VaiOnko/gould-k20/pictures/exterior/bottom.jpg

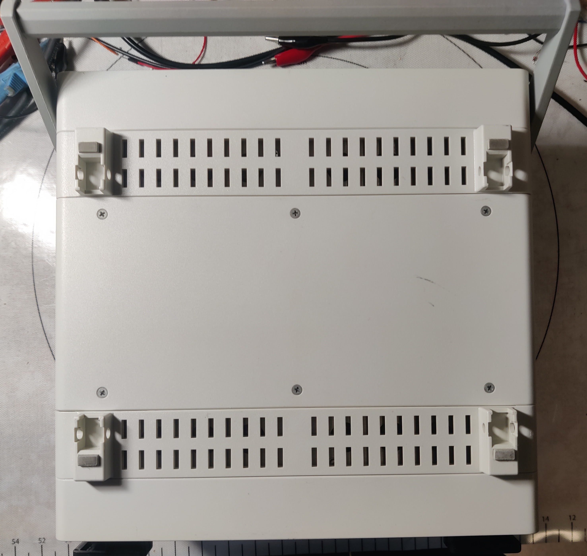
pictures/exterior/bottom.jpg
