VaiOnko/gould-k20/pictures/exterior/top.jpg

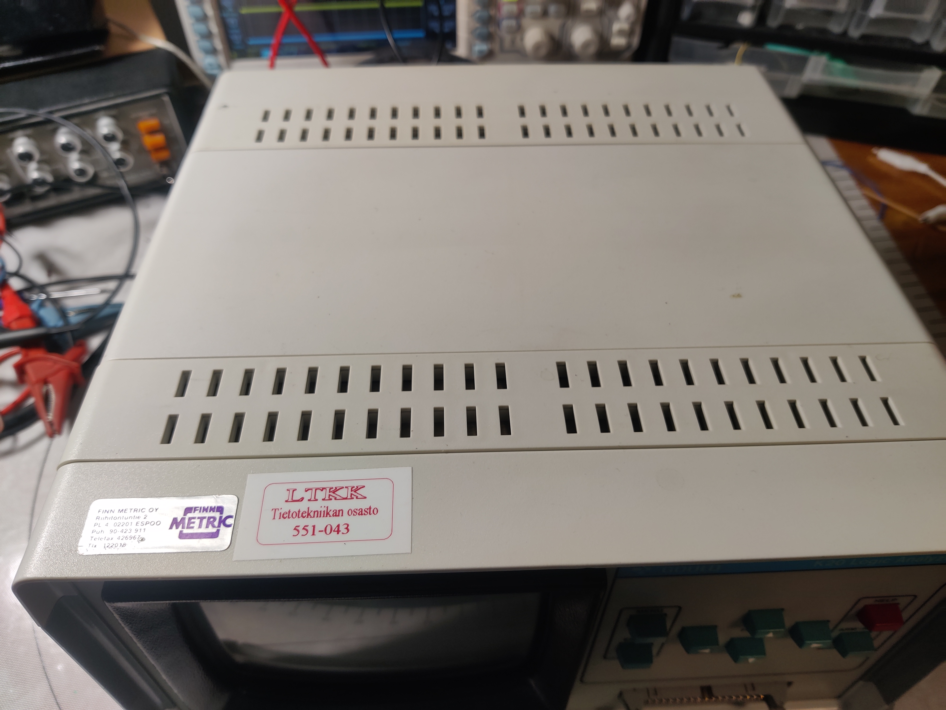
pictures/exterior/top.jpg
