VaiOnko/gould-k20/pictures/interior/acquisition-board-2.jpg

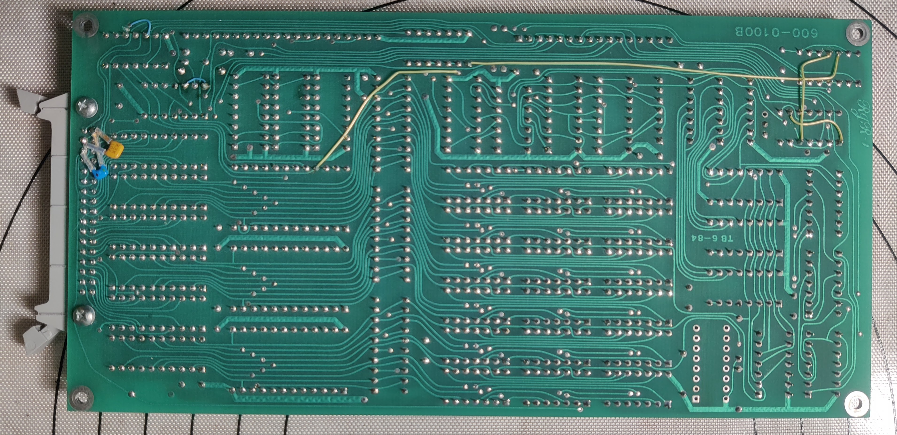
pictures/interior/acquisition-board-2.jpg
