VaiOnko/gould-k20/pictures/interior/cpu-board-1.jpg

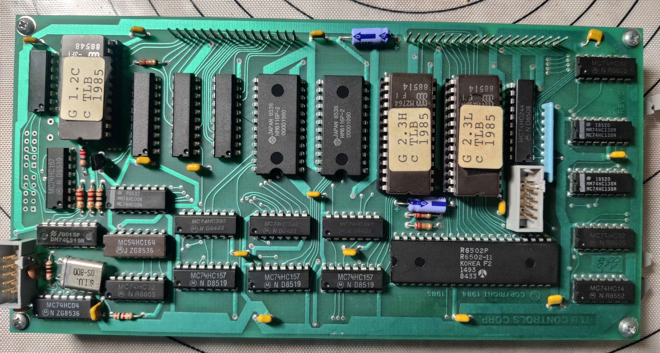
pictures/interior/cpu-board-1.jpg
