VaiOnko/gould-k20/pictures/interior/cpu-board-2.jpg

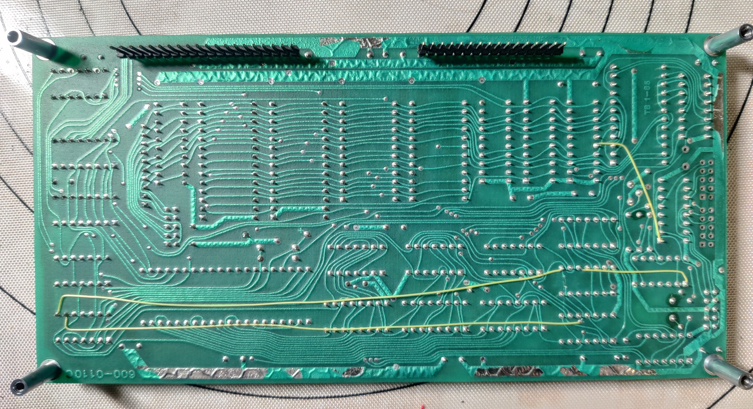
pictures/interior/cpu-board-2.jpg
