VaiOnko/gould-k20/pictures/menus/menu11.jpg

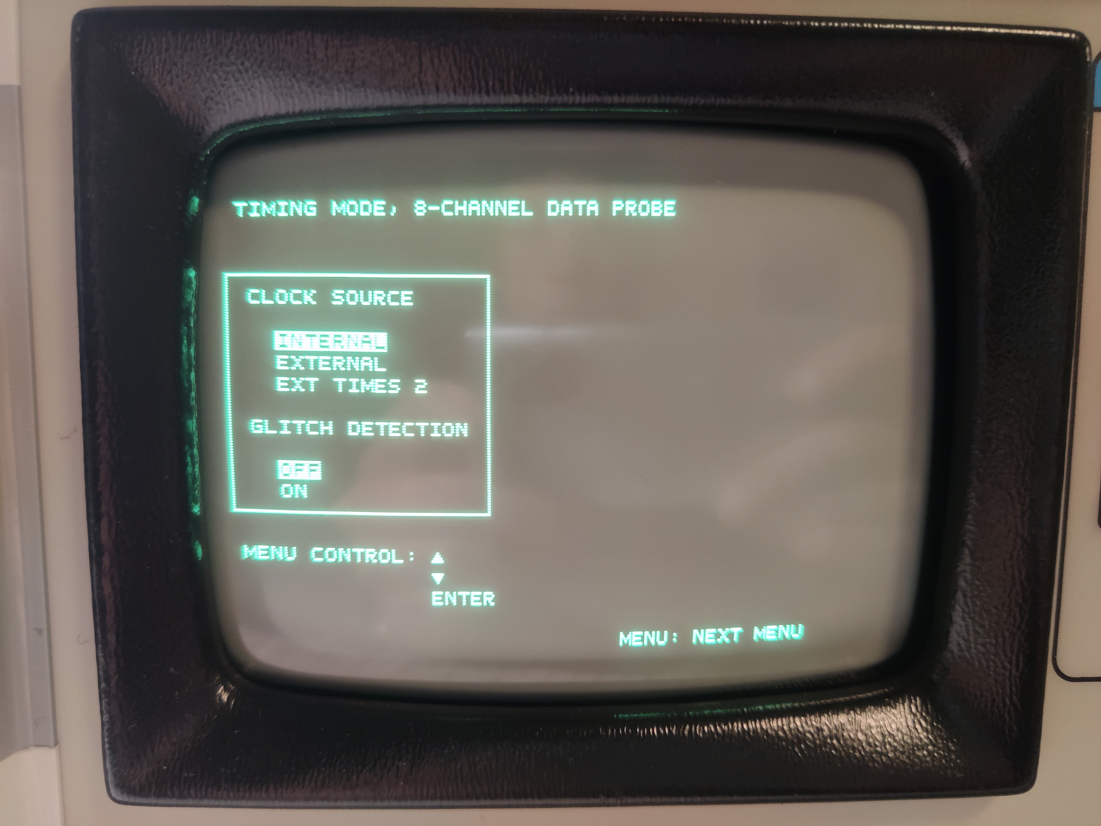
pictures/menus/menu11.jpg
