VaiOnko/gould-k20/pictures/menus/menu12.jpg

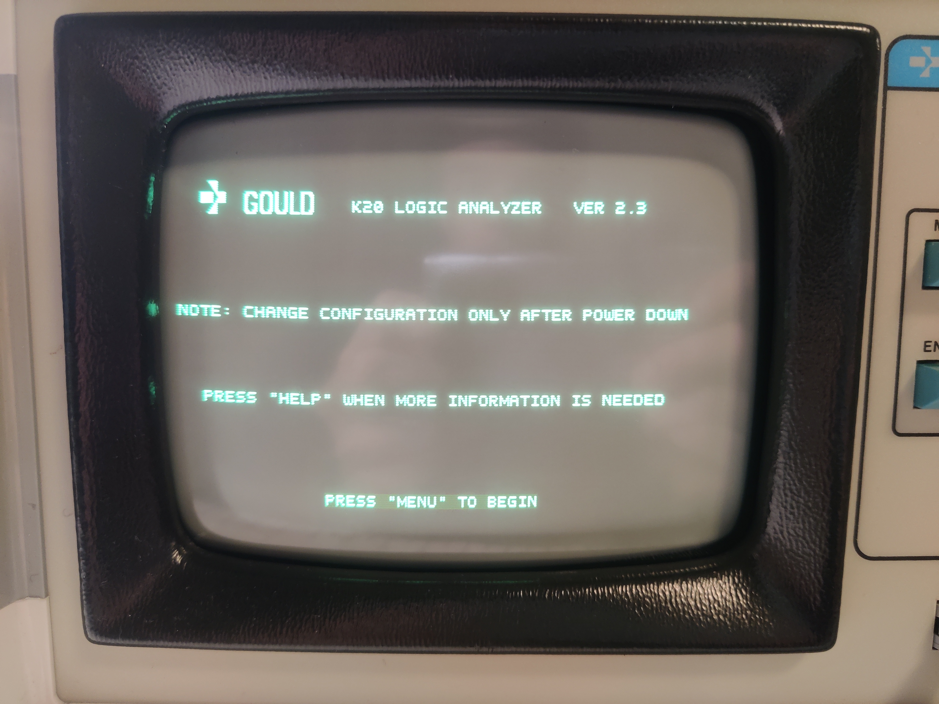
pictures/menus/menu12.jpg
